Anrannarl/Lighthouse-Tracker-RP2040/Miscellaneous/MPU6050.JPG

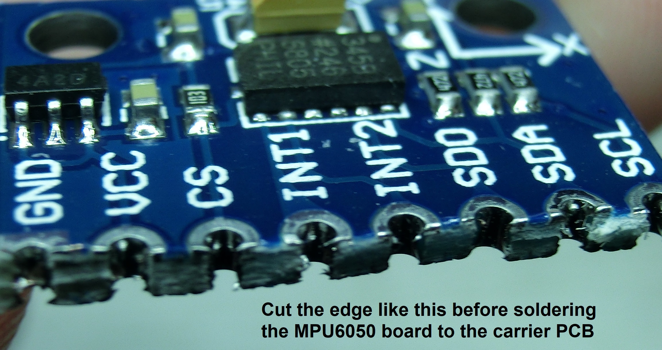
Miscellaneous/MPU6050.JPG
