Anrannarl/Lighthouse-Tracker-RP2040/Manufacturing Files/Lighthouse Sensor Carrier/Preview2.png

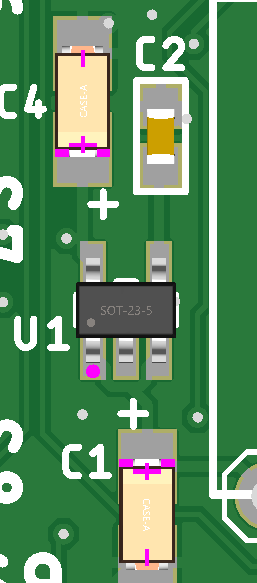
Manufacturing Files/Lighthouse Sensor Carrier/Preview2.png
