Anrannarl/Lighthouse-Tracker-RP2040/Manufacturing Files/Lighthouse Sensor/Preview.png

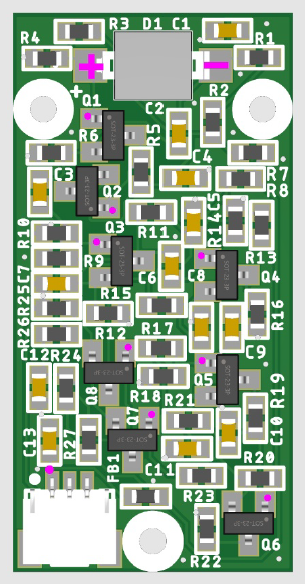
Manufacturing Files/Lighthouse Sensor/Preview.png
