Anrannarl/Lighthouse-Tracker-RP2040/Manufacturing Files/Lighthouse Tracker/Preview1.png

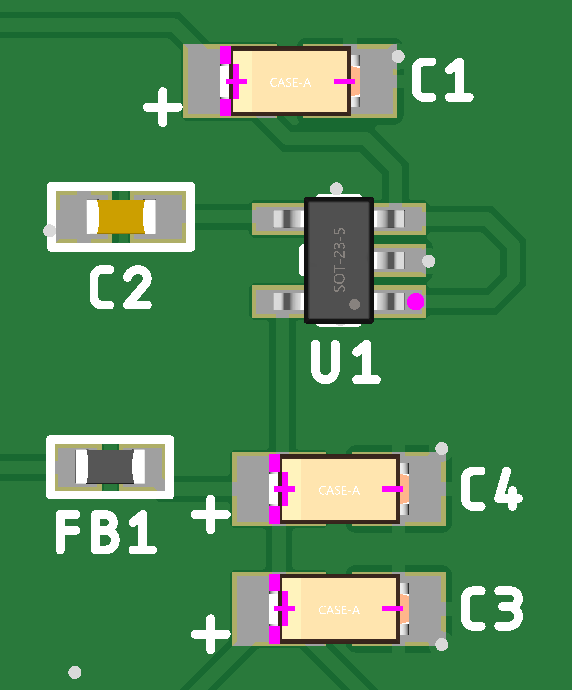
Manufacturing Files/Lighthouse Tracker/Preview1.png
